mckacz/mini-itx-nas-case/stl/passive_mini_itx/case_panel_back.stl

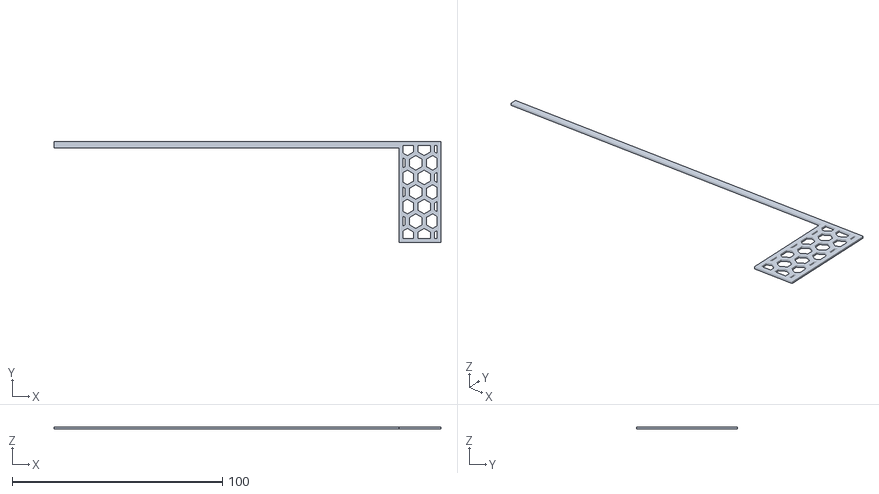
[picture p28: CAD file, 2024-10-26]
stl/passive_mini_itx/case_panel_back.stl
184.0 x 48.0 x 1.00
