mckacz/mini-itx-nas-case/stl/passive_mini_itx_2x3.5_hdd_fan_lcd/case_top_cap.stl

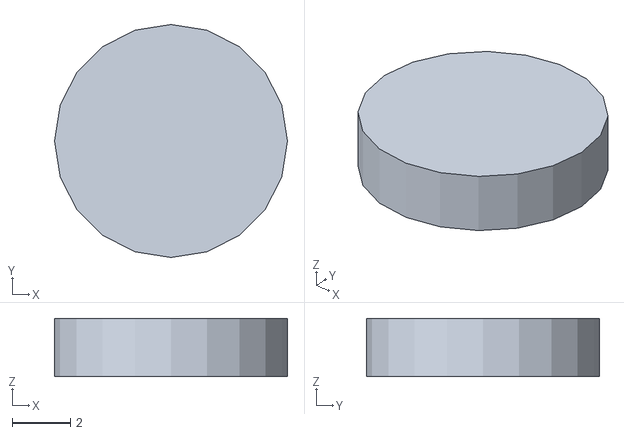
[picture p29: CAD file, 2024-10-26]
stl/passive_mini_itx_2x3.5_hdd_fan_lcd/case_top_cap.stl
8.00 x 8.00 x 2.00
