mckacz/mini-itx-nas-case/stl/passive_mini_itx/case_pillar.stl

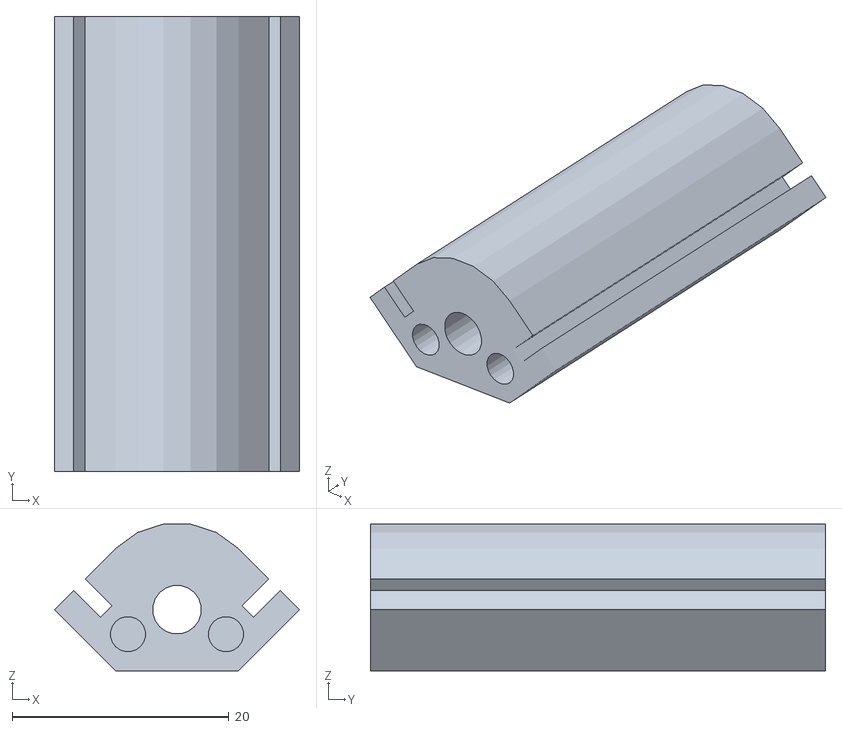
[picture p30: CAD file, 2024-10-26]
stl/passive_mini_itx/case_pillar.stl
22.6 x 42.0 x 13.6
