mckacz/mini-itx-nas-case/stl/passive_mini_itx_2x3.5_hdd_fan_lcd/case_panel_front.stl

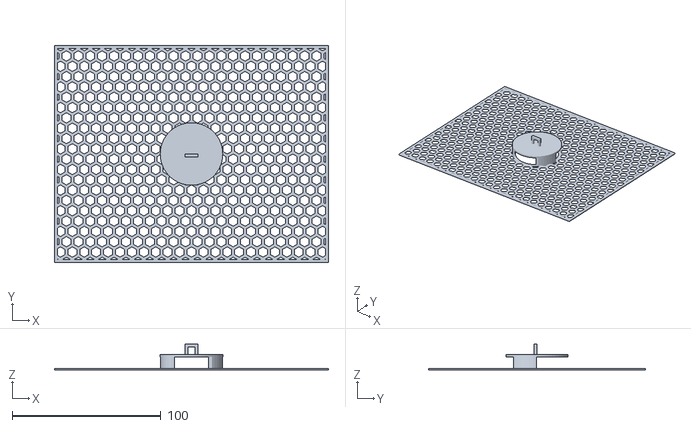
[picture p31: CAD file, 2024-10-26]
stl/passive_mini_itx_2x3.5_hdd_fan_lcd/case_panel_front.stl
184.0 x 146.0 x 17.2
